arduilex/SAE-pince-industrielle/python/VL53L0X.py

#!/usr/bin/python
import time
from ctypes import *
import smbus

i2cbus = smbus.SMBus(1)

# i2c bus read callback
def i2c_read(address, reg, data_p, length):
    ret_val = 0;
    result = []
 
    try:
        result = i2cbus.read_i2c_block_data(address, reg, length)
    except IOError:
        ret_val = -1;


    if (ret_val == 0):
        for index in range(length):
            data_p[index] = result[index]

    return ret_val

# i2c bus write callback
def i2c_write(address, reg, data_p, length):
    ret_val = 0;
    data = []

    for index in range(length):
        data.append(data_p[index])
    try:
        i2cbus.write_i2c_block_data(address, reg, data)
    except IOError:
        ret_val = -1; 

    return ret_val

# Load VL53L0X shared lib 
tof_lib = CDLL("./VL53L0X_rasp_python/bin/vl53l0x_python.so")

# Create read function pointer
READFUNC = CFUNCTYPE(c_int, c_ubyte, c_ubyte, POINTER(c_ubyte), c_ubyte)
read_func = READFUNC(i2c_read)

# Create write function pointer
WRITEFUNC = CFUNCTYPE(c_int, c_ubyte, c_ubyte, POINTER(c_ubyte), c_ubyte)
write_func = WRITEFUNC(i2c_write)

# pass i2c read and write function pointers to VL53L0X library
tof_lib.VL53L0X_set_i2c(read_func, write_func)

class CapteurTof(object):
    """VL53L0X ToF."""

    object_number = 0

    def __init__(self, address=0x29, TCA9548A_Num=255, TCA9548A_Addr=0, **kwargs):
        """Initialize the VL53L0X ToF Sensor from ST"""
        self.device_address = address
        self.TCA9548A_Device = TCA9548A_Num 
        self.TCA9548A_Address = TCA9548A_Addr
        self.my_object_number = CapteurTof.object_number
        CapteurTof.object_number += 1

    def start_ranging(self, mode="beter"):
        """Start VL53L0X ToF Sensor Ranging"""
        # Ajout perso
        mode_list = ["good", "beter", "best", "long", "speed"]
        mode = mode_list.index(mode)
        tof_lib.startRanging(self.my_object_number, mode, self.device_address, self.TCA9548A_Device, self.TCA9548A_Address)

    def stop_ranging(self):
        """Stop VL53L0X ToF Sensor Ranging"""
        tof_lib.stopRanging(self.my_object_number)

    def get_distance(self):
        """Get distance from VL53L0X ToF Sensor in mm"""
        return tof_lib.getDistance(self.my_object_number)

    # This function included to show how to access the ST library directly
    # from python instead of through the simplified interface
    def get_timing(self):
        Dev = POINTER(c_void_p)
        Dev = tof_lib.getDev(self.my_object_number)
        budget = c_uint(0)
        budget_p = pointer(budget)
        Status =  tof_lib.VL53L0X_GetMeasurementTimingBudgetMicroSeconds(Dev, budget_p)
        if (Status == 0):
            if budget.value + 1000 < 20000:
                return 0.02
            else:
                return (budget.value + 1000)/1000000.00
        else:
            return 0.02
